andykarpov/MobyAMP/build/pdf/tda1557q_v_1_0_pcb_bottom.pdf

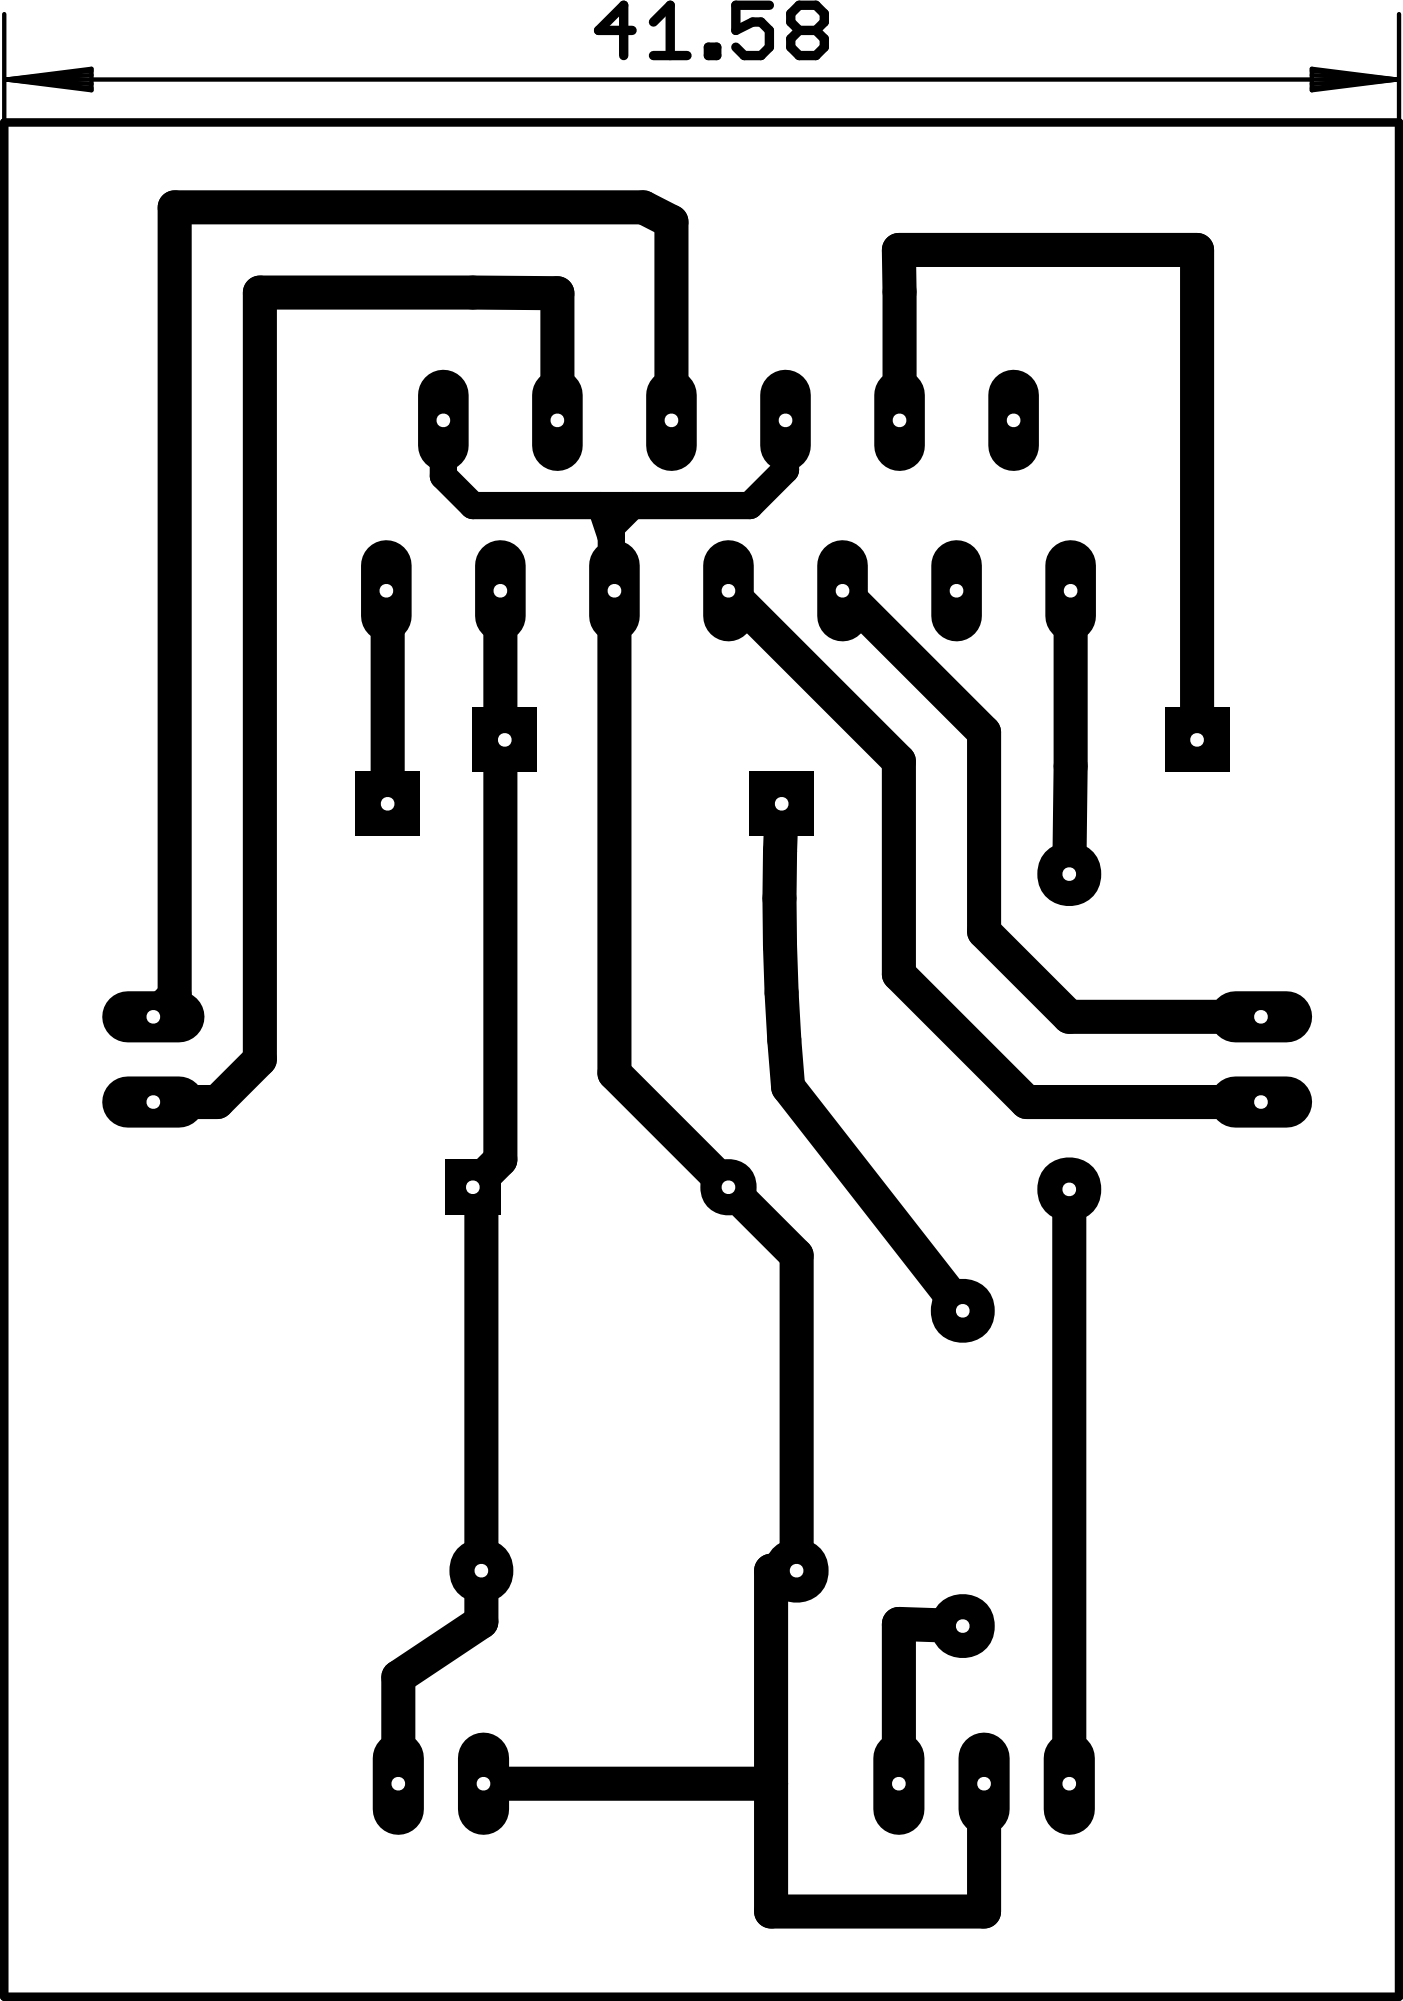
[picture p15: page 1]
