andykarpov/MobyAMP/build/pdf/tda1557q_v_1_0_pcb_cmp.pdf

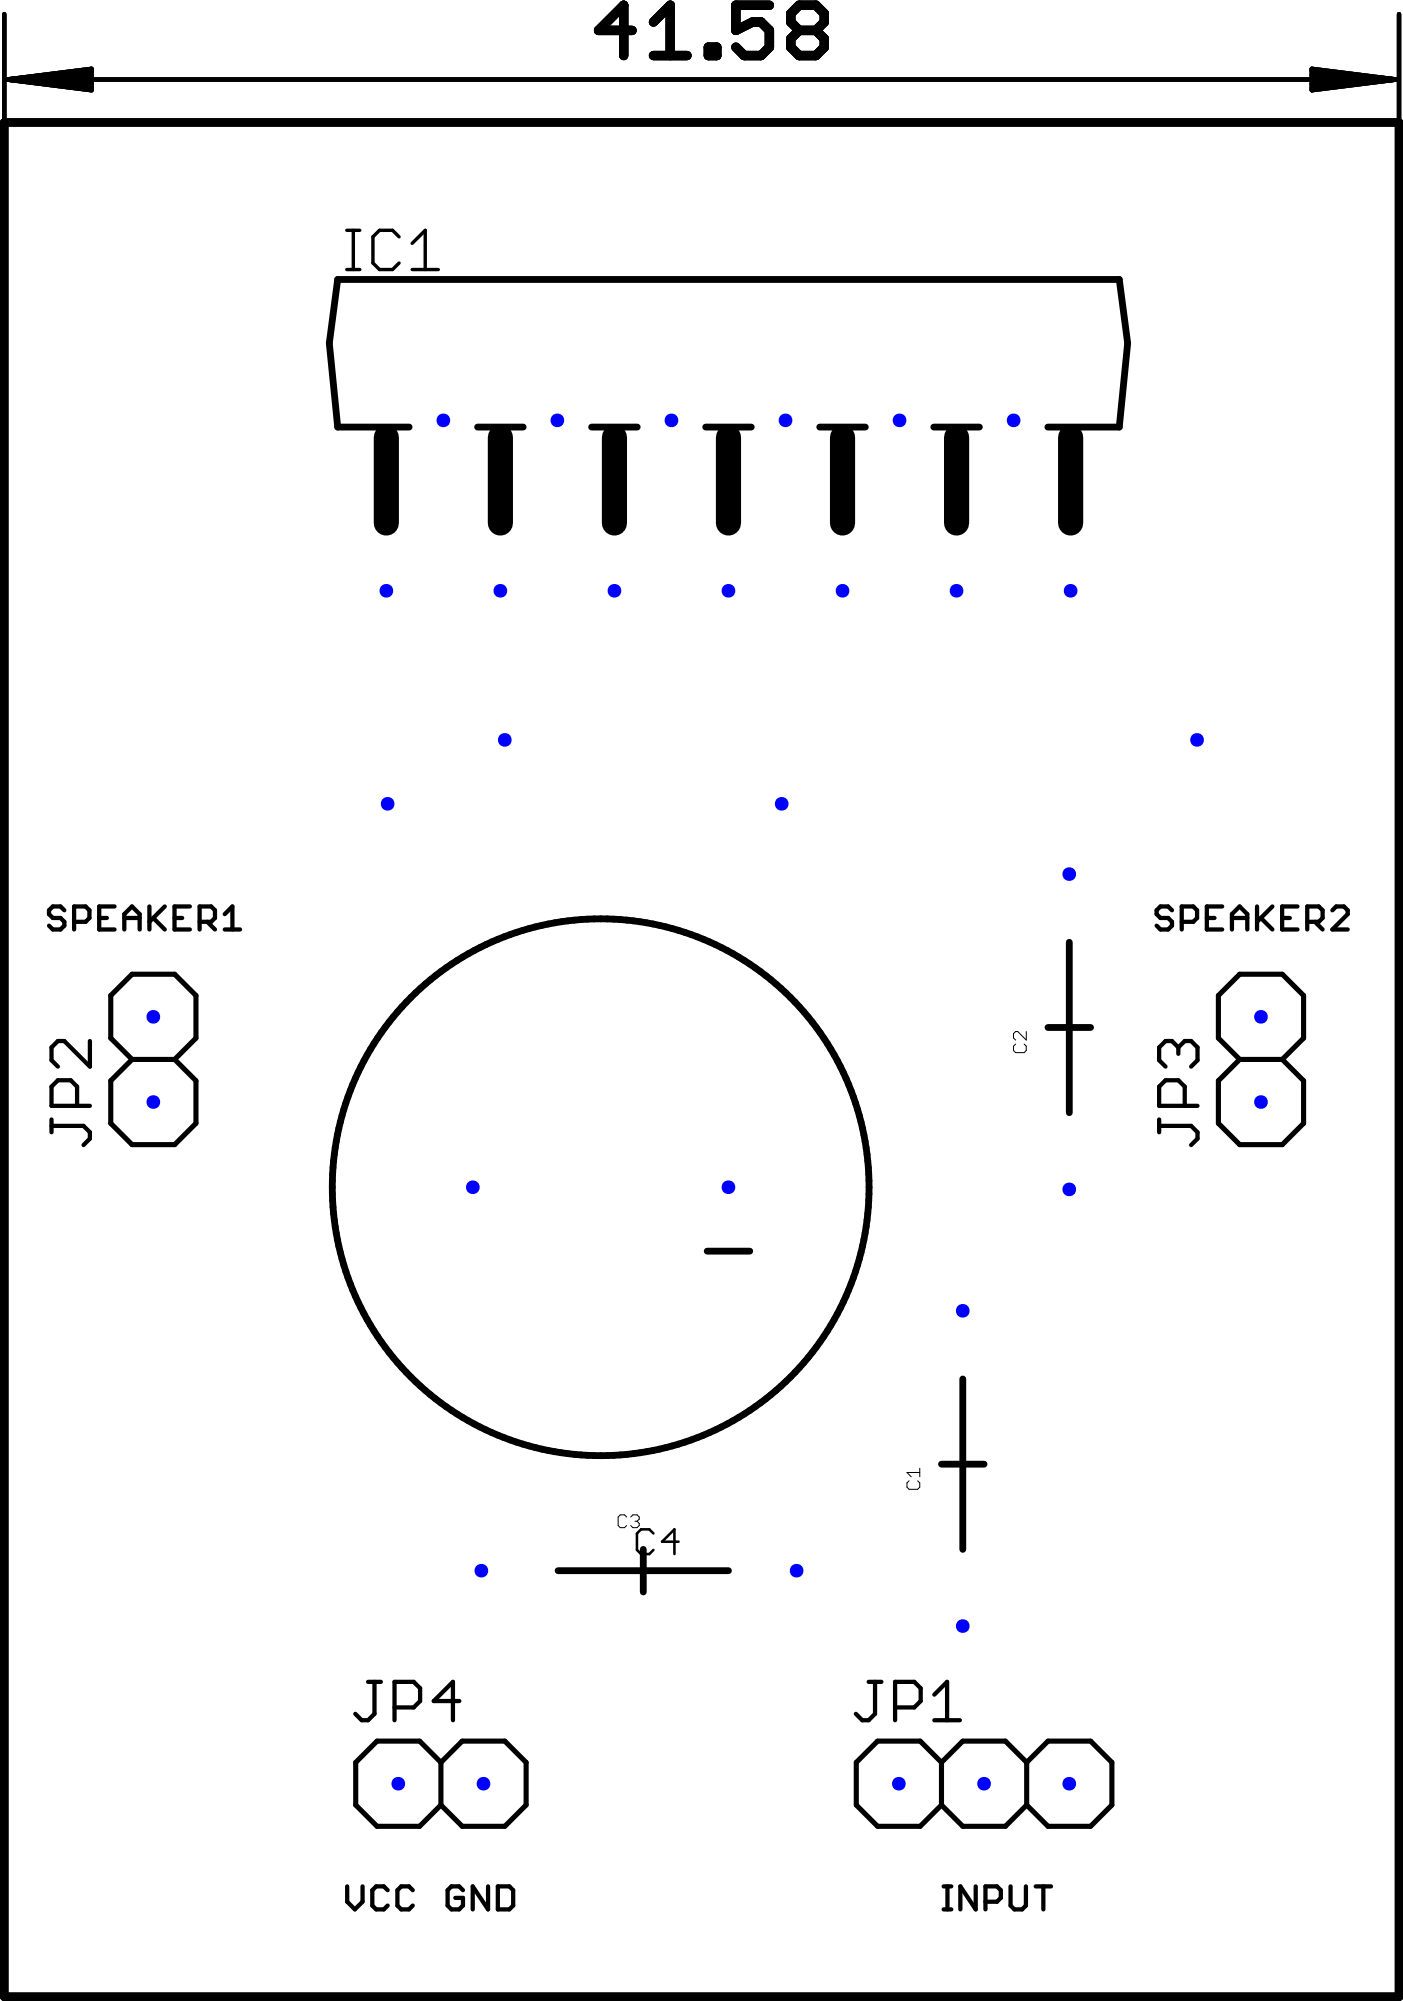
[picture p16: page 1]
