andykarpov/MobyAMP/build/pdf/tda1557q_v_1_0_pcb_top.pdf

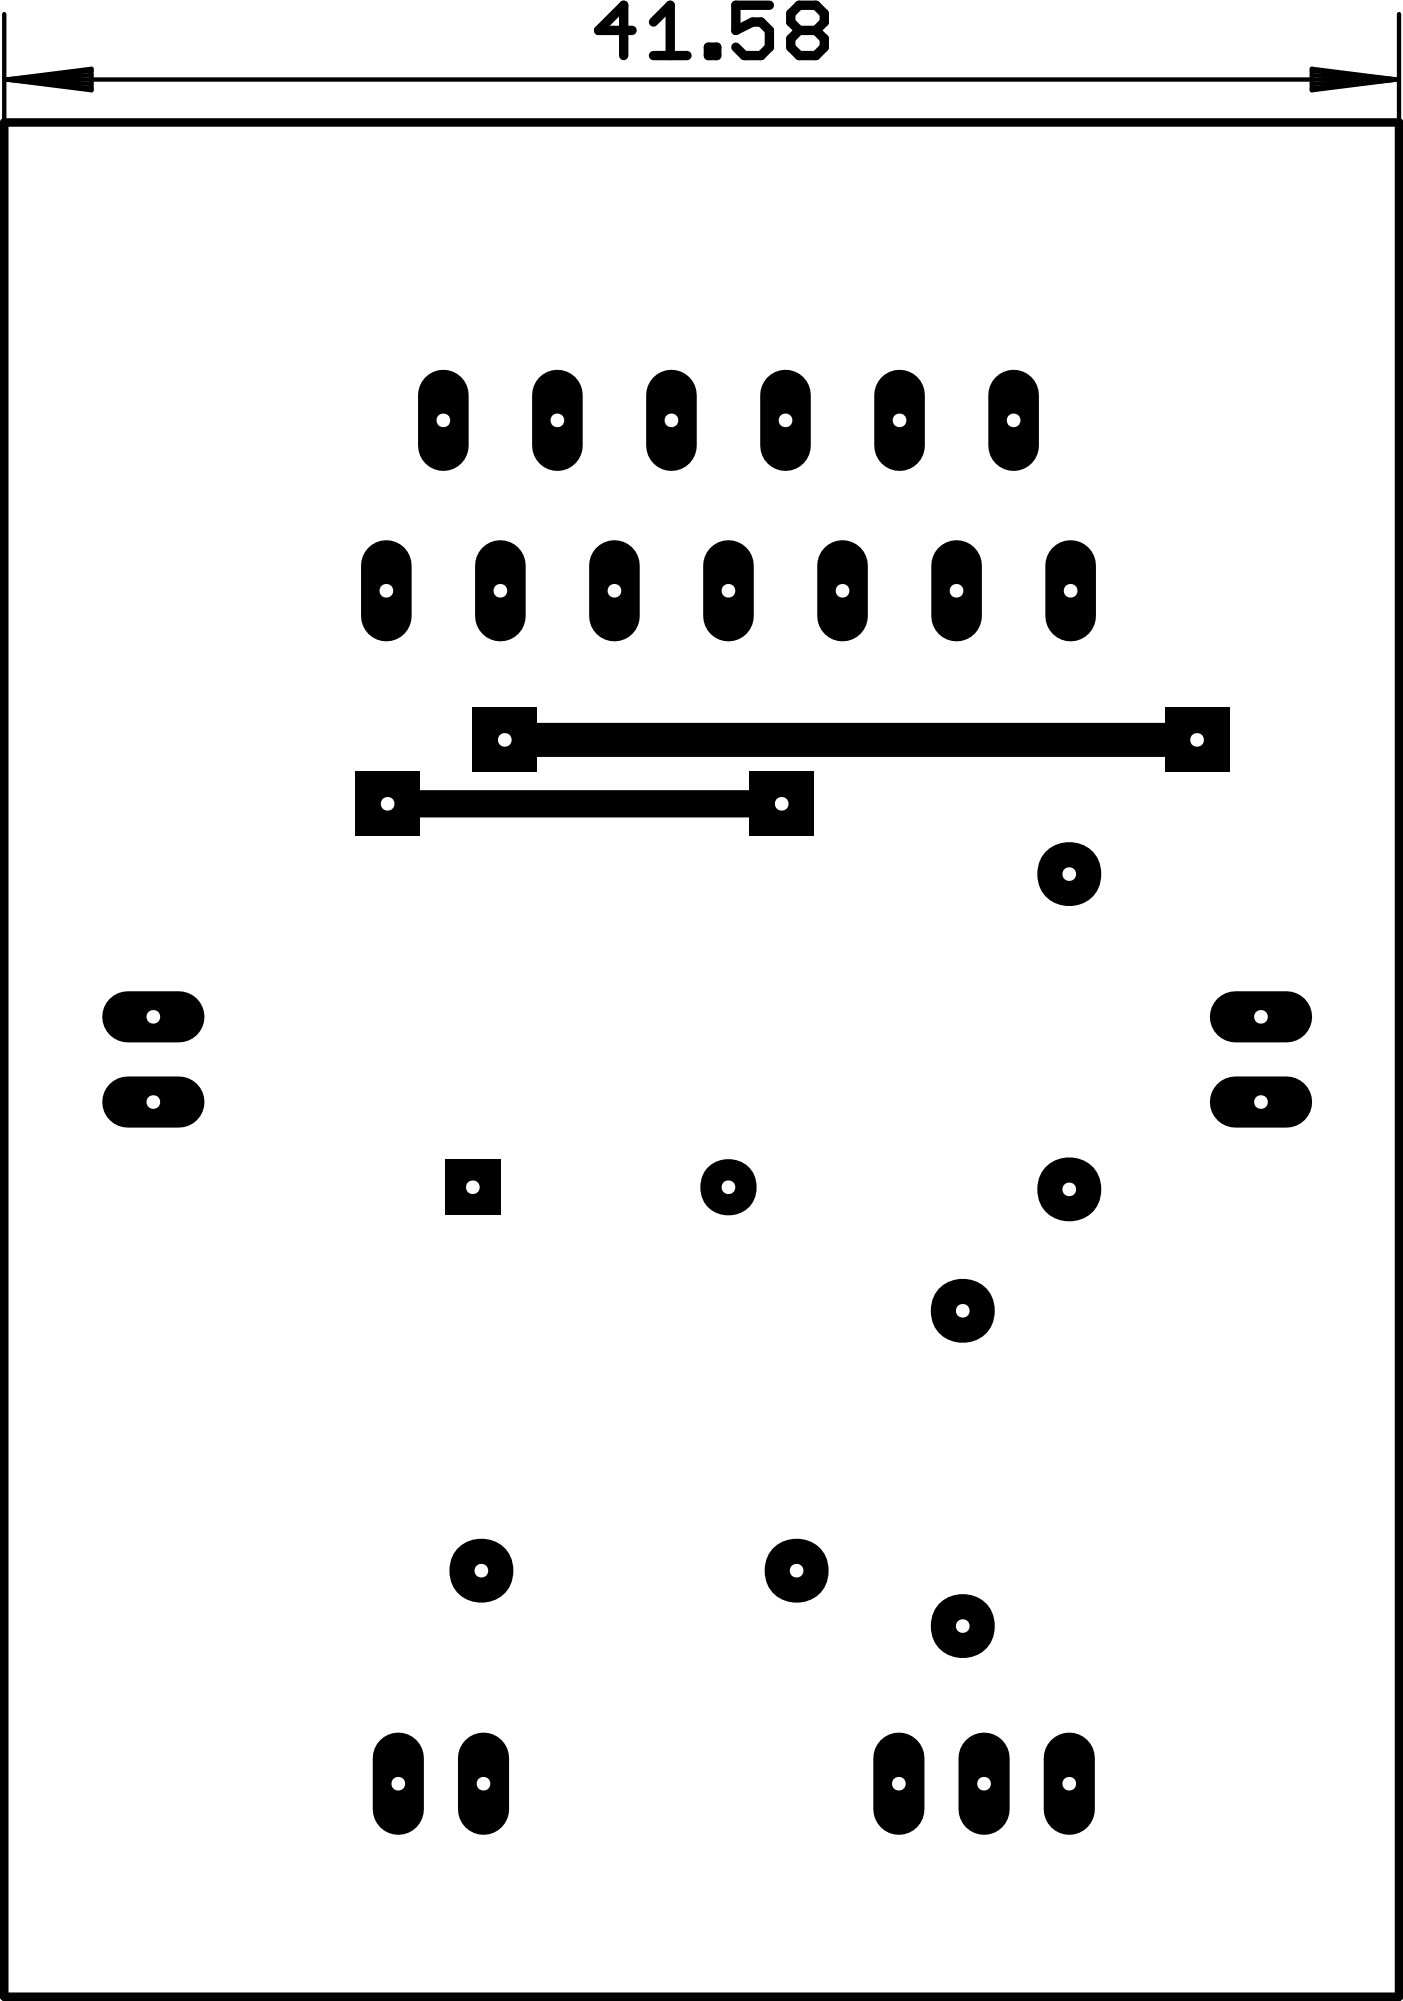
[picture p17: page 1]
