andykarpov/MobyAMP/build/pdf/tda2030a_v_1_0_pcb_bottom.pdf

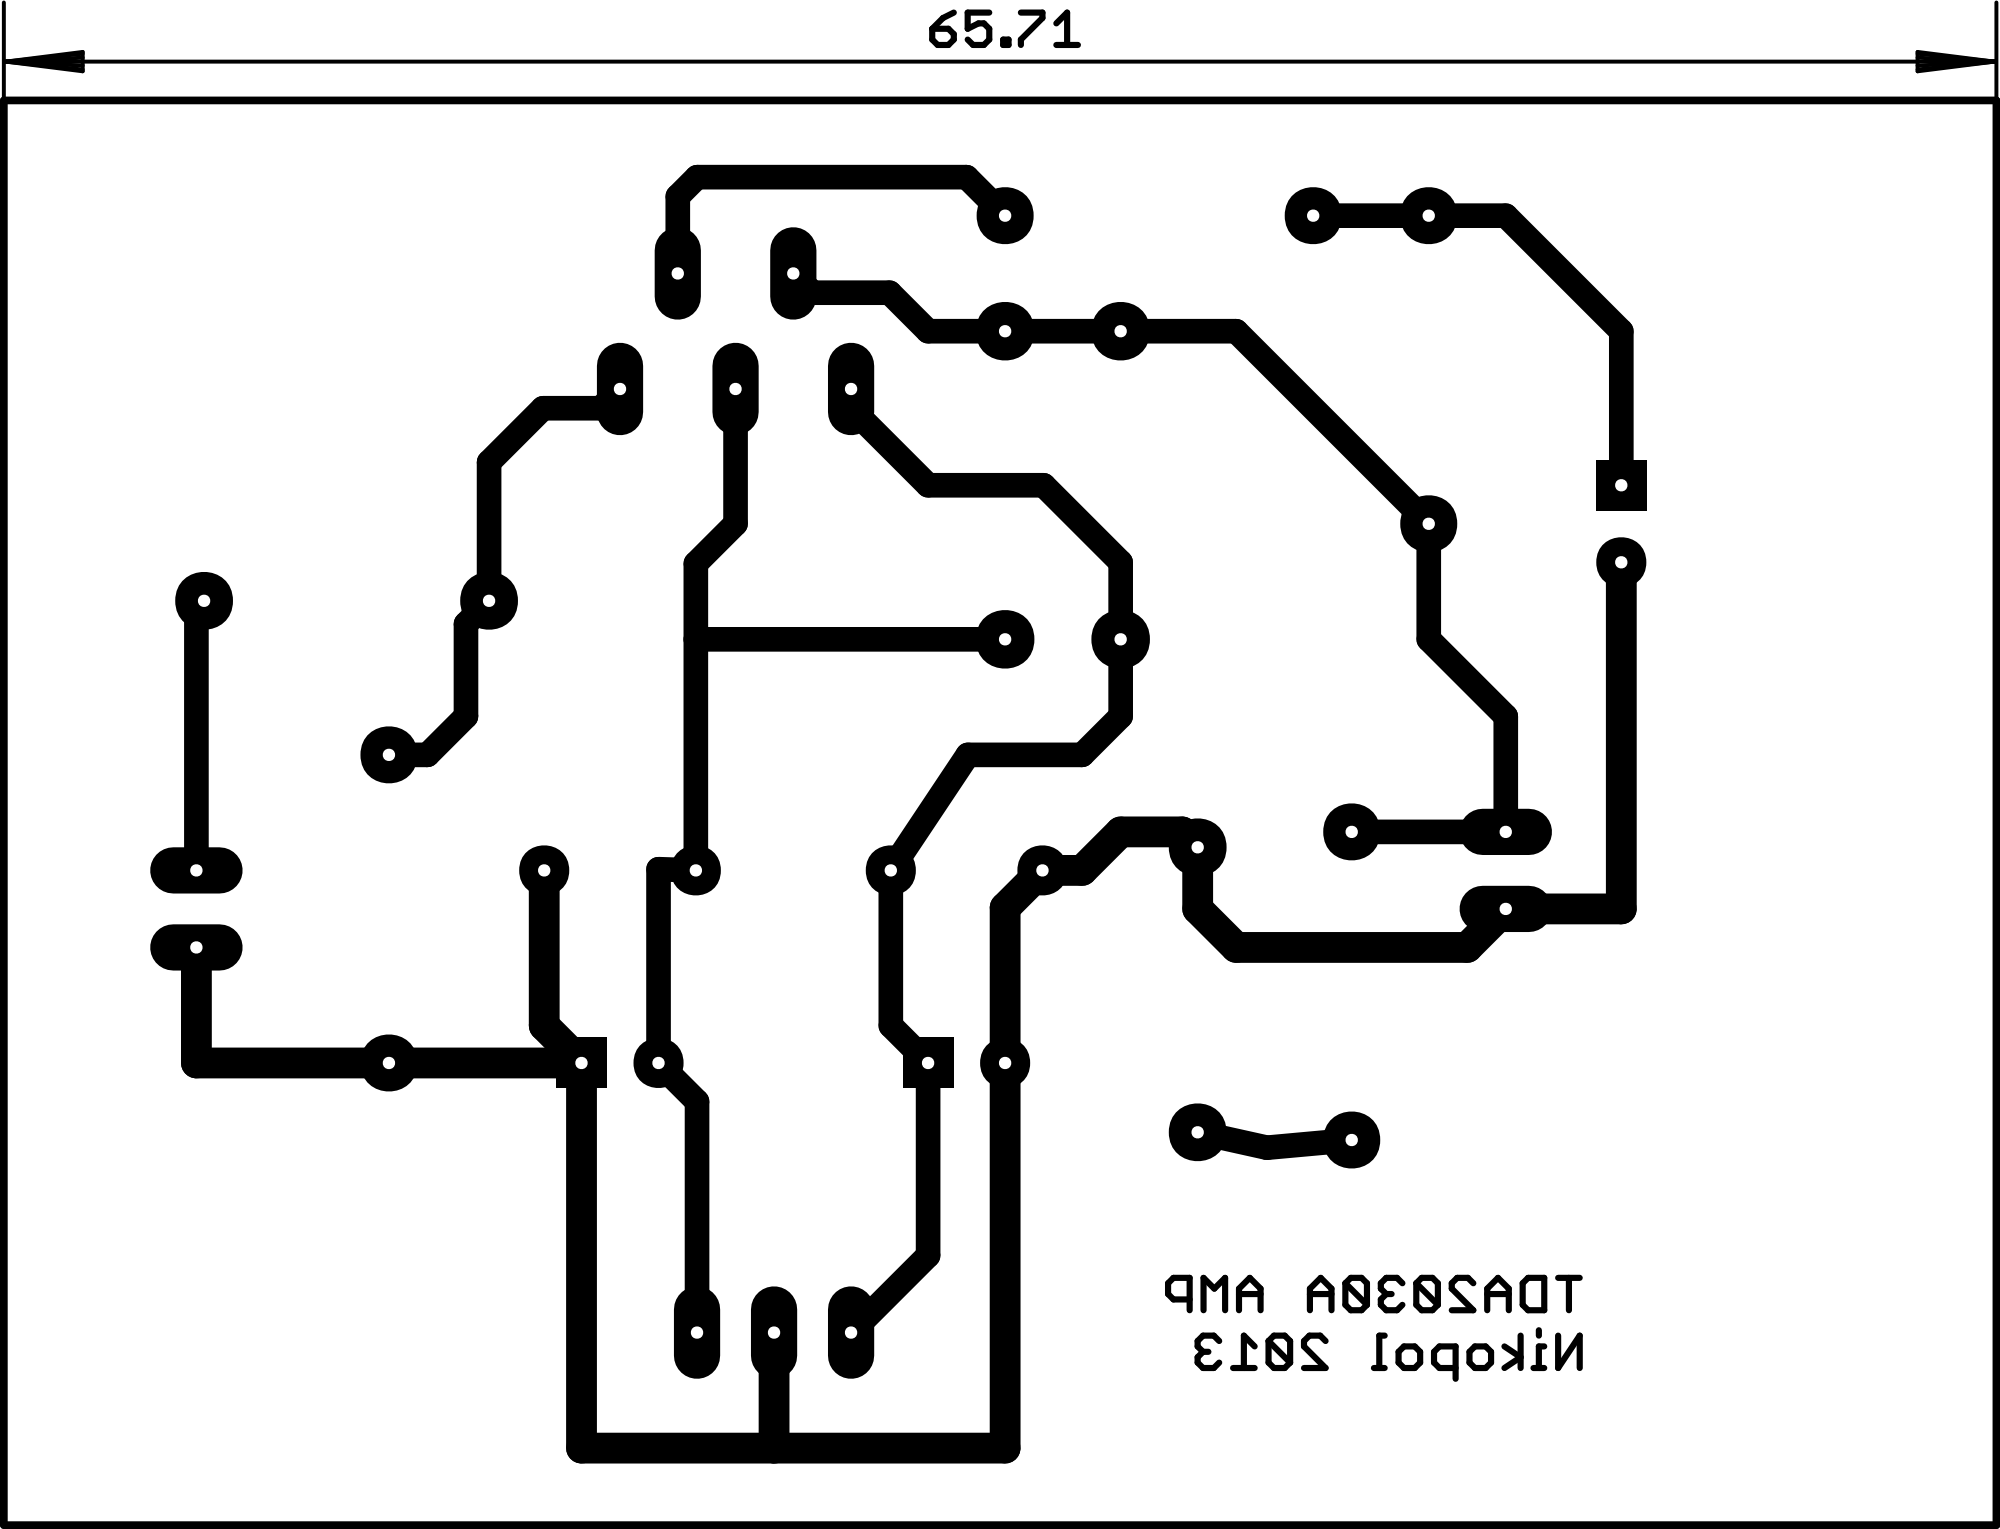
[picture p18: page 1]
