andykarpov/MobyAMP/build/pdf/tda2030a_v_1_0_pcb_cmp.pdf

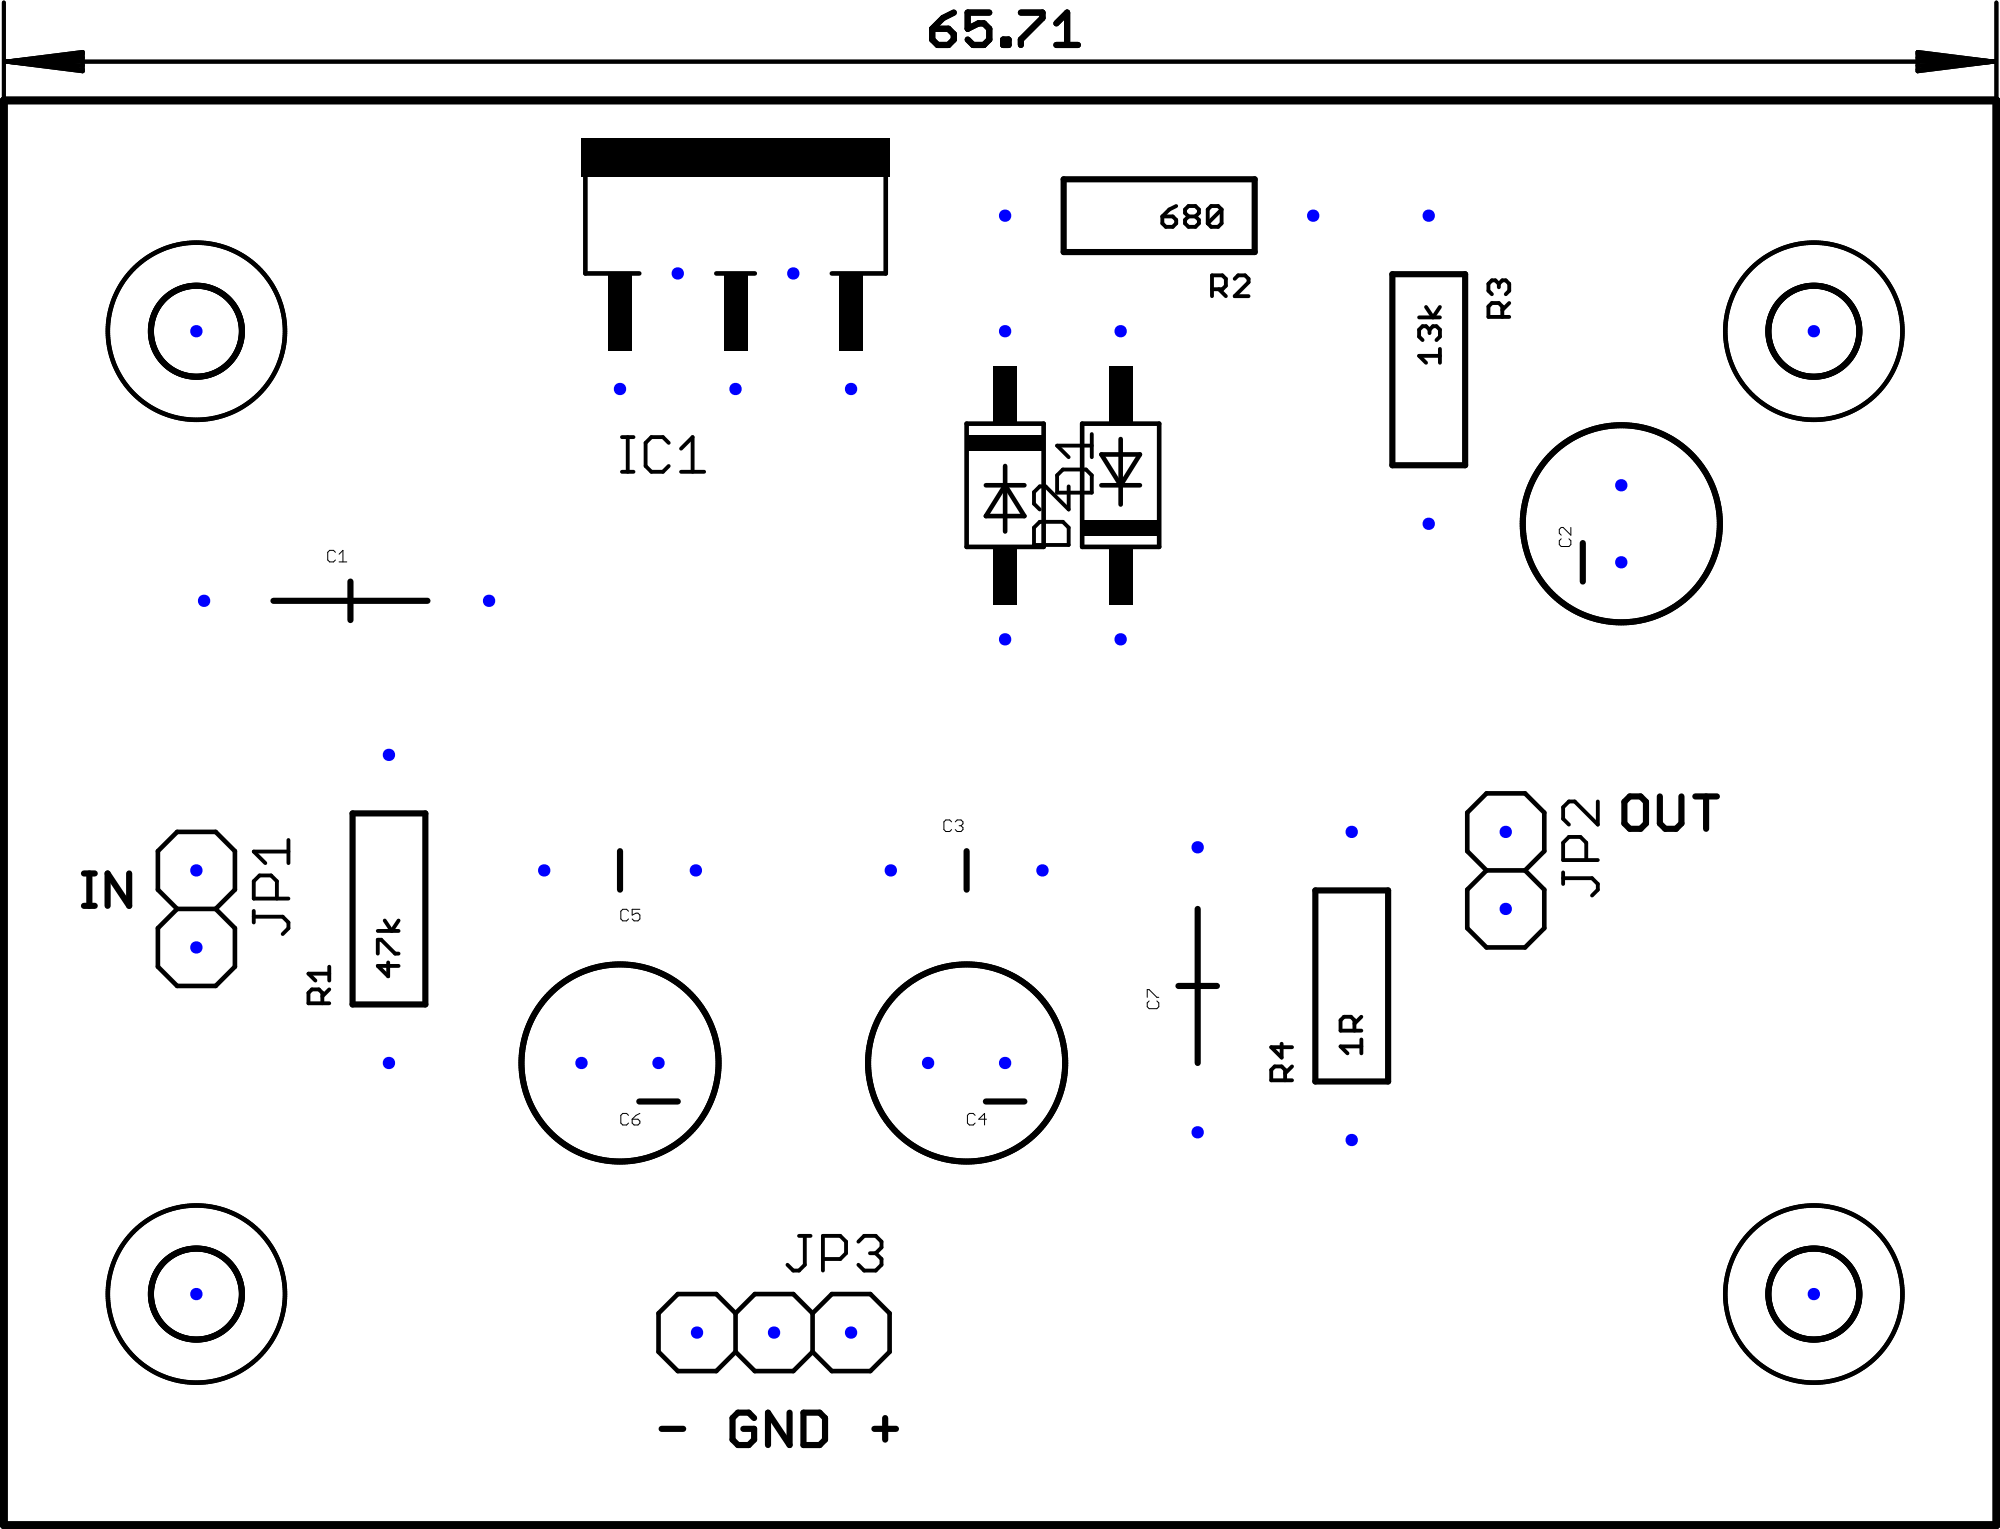
[picture p19: page 1]
