andykarpov/MobyAMP/build/pdf/tda2030a_v_1_0_pcb_top.pdf

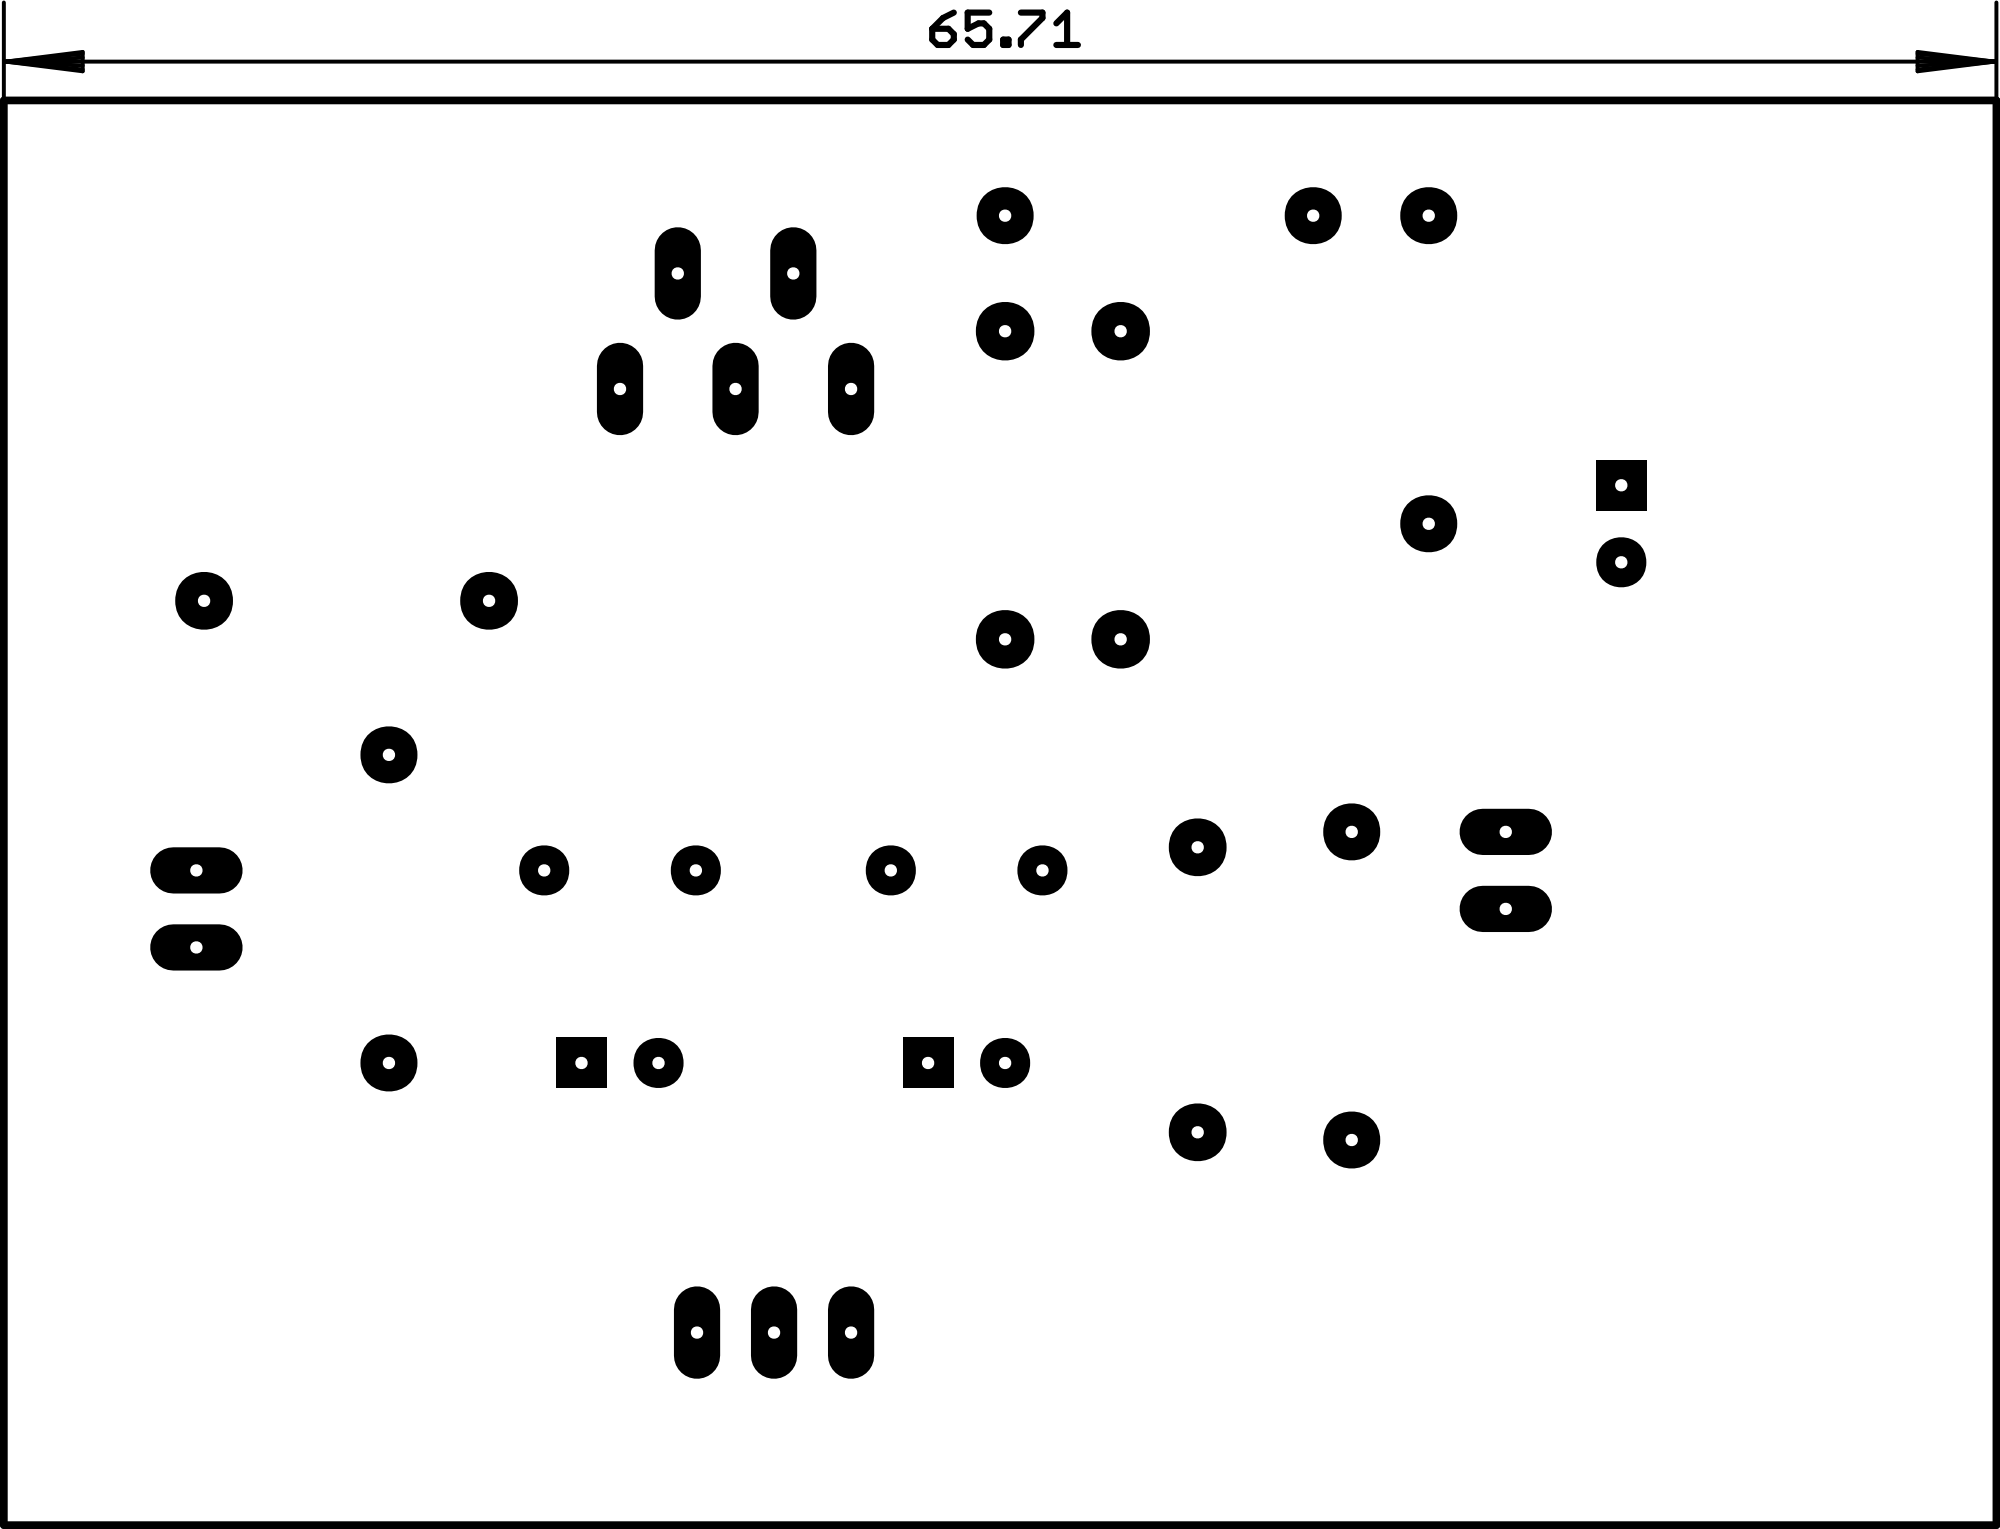
[picture p20: page 1]
