andykarpov/MobyAMP/interface2/amp_interface2_v_1_0.pdf

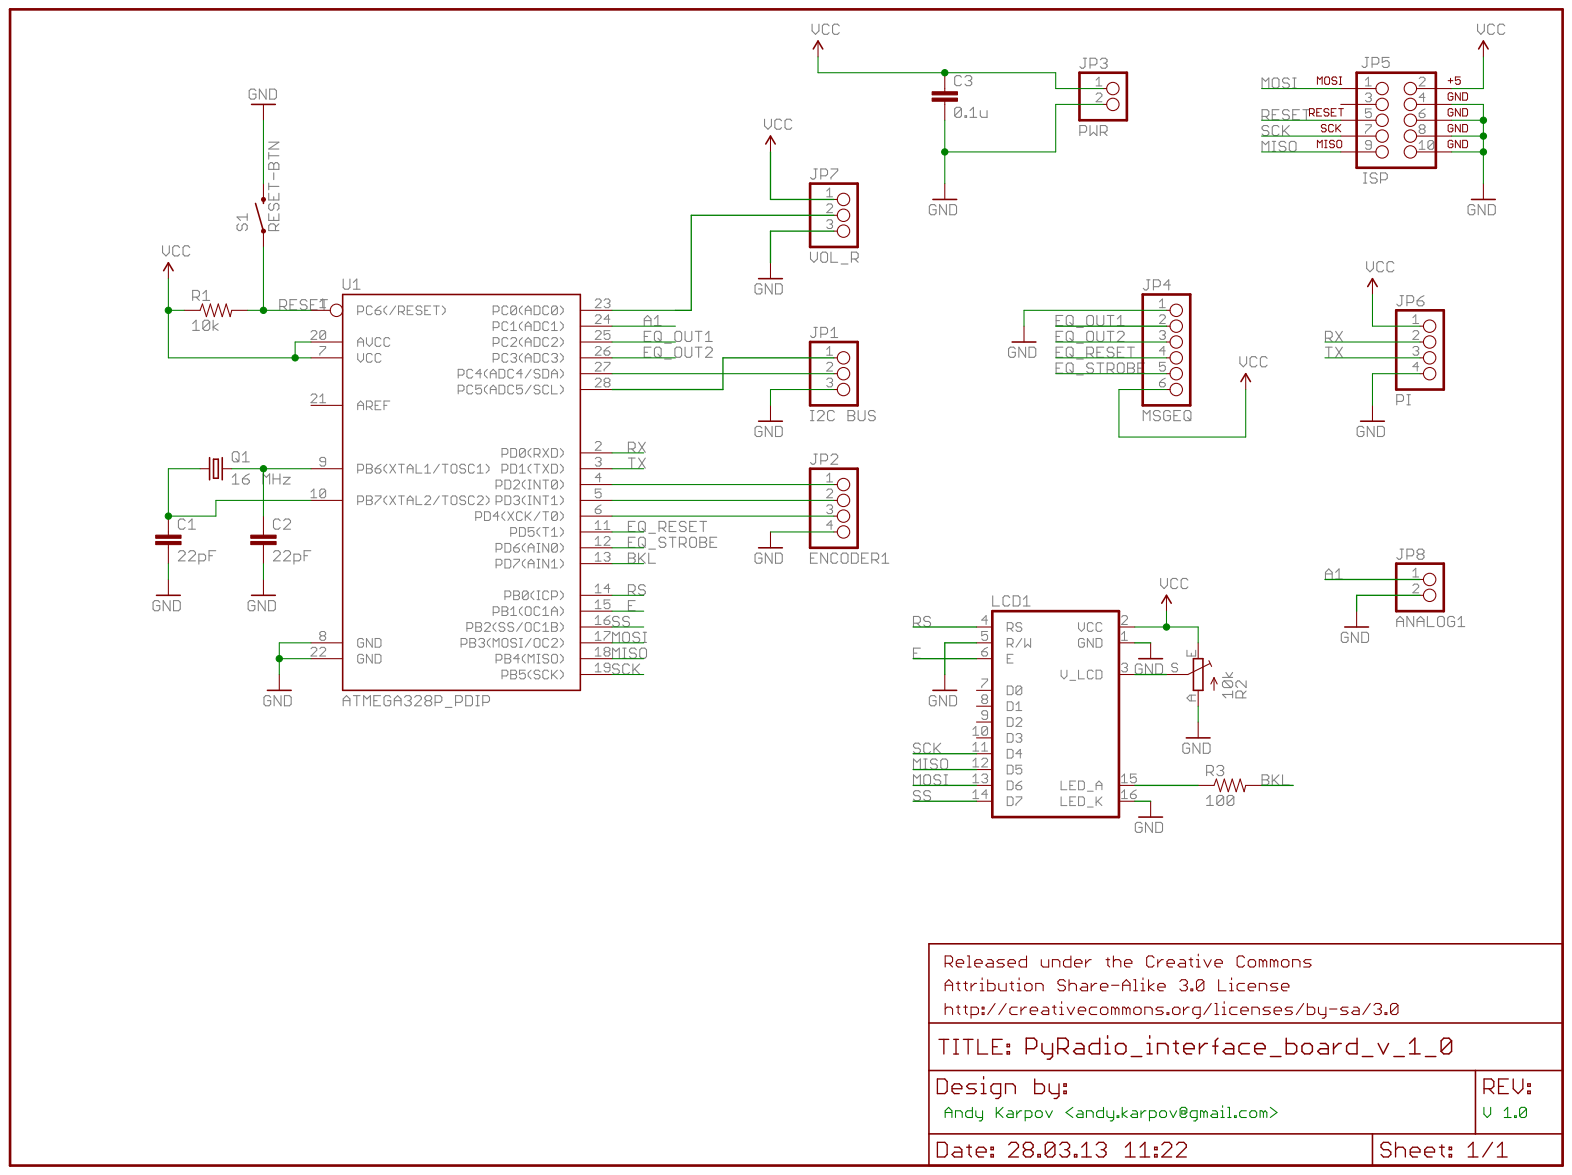
[picture p21: page 1]
