andykarpov/MobyAMP/msgeq7/amp_msgeq7_v_1_0.pdf

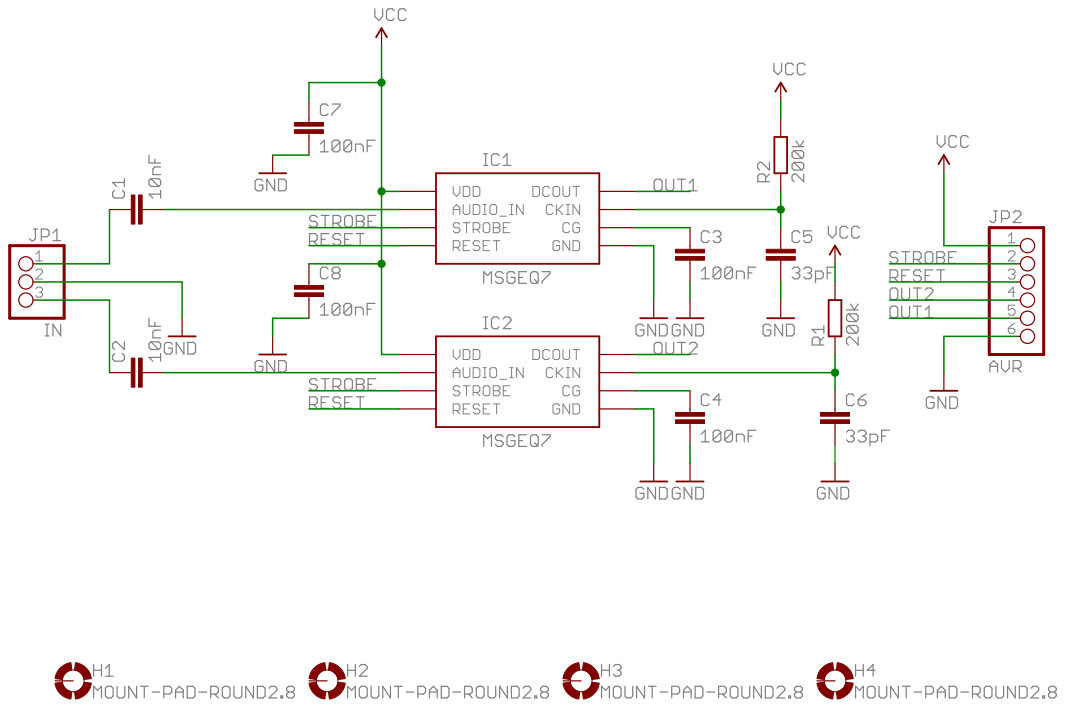
[picture p22: page 1]
