andykarpov/MobyAMP/pt2322/amp_pt2322_v_1_0.pdf

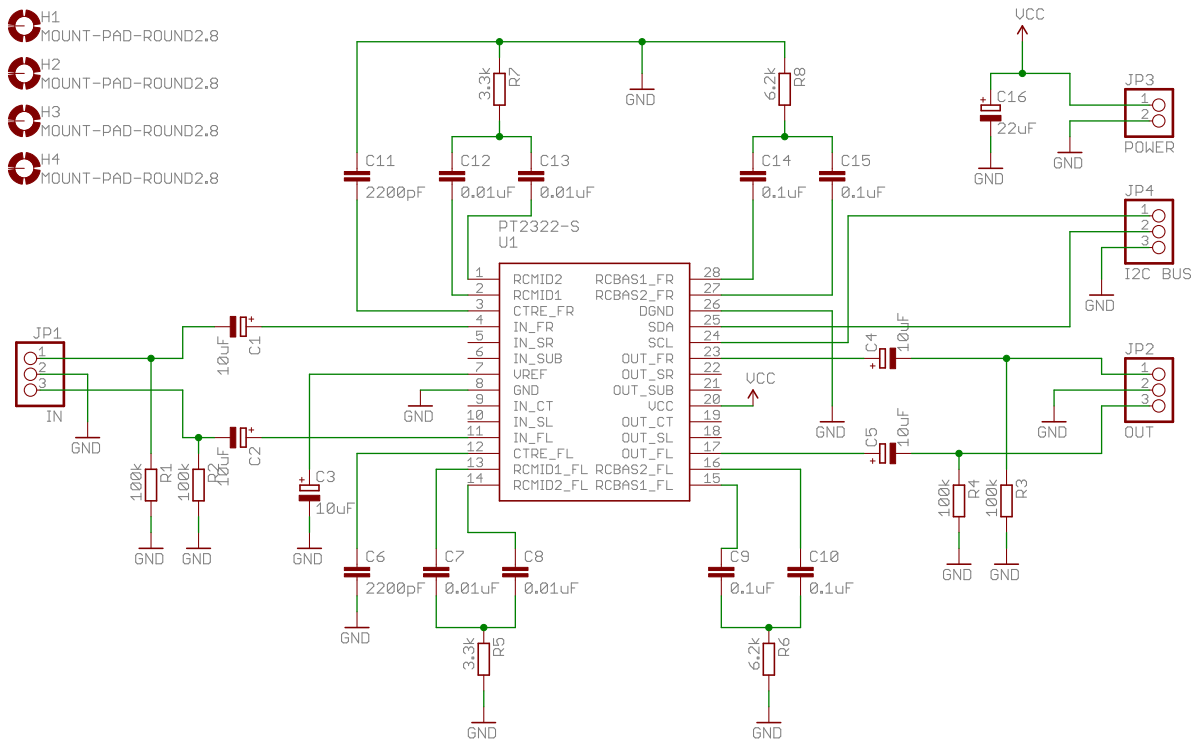
[picture p23: page 1]
