andykarpov/MobyAMP/interface/amp_interface_v_1_0.pdf

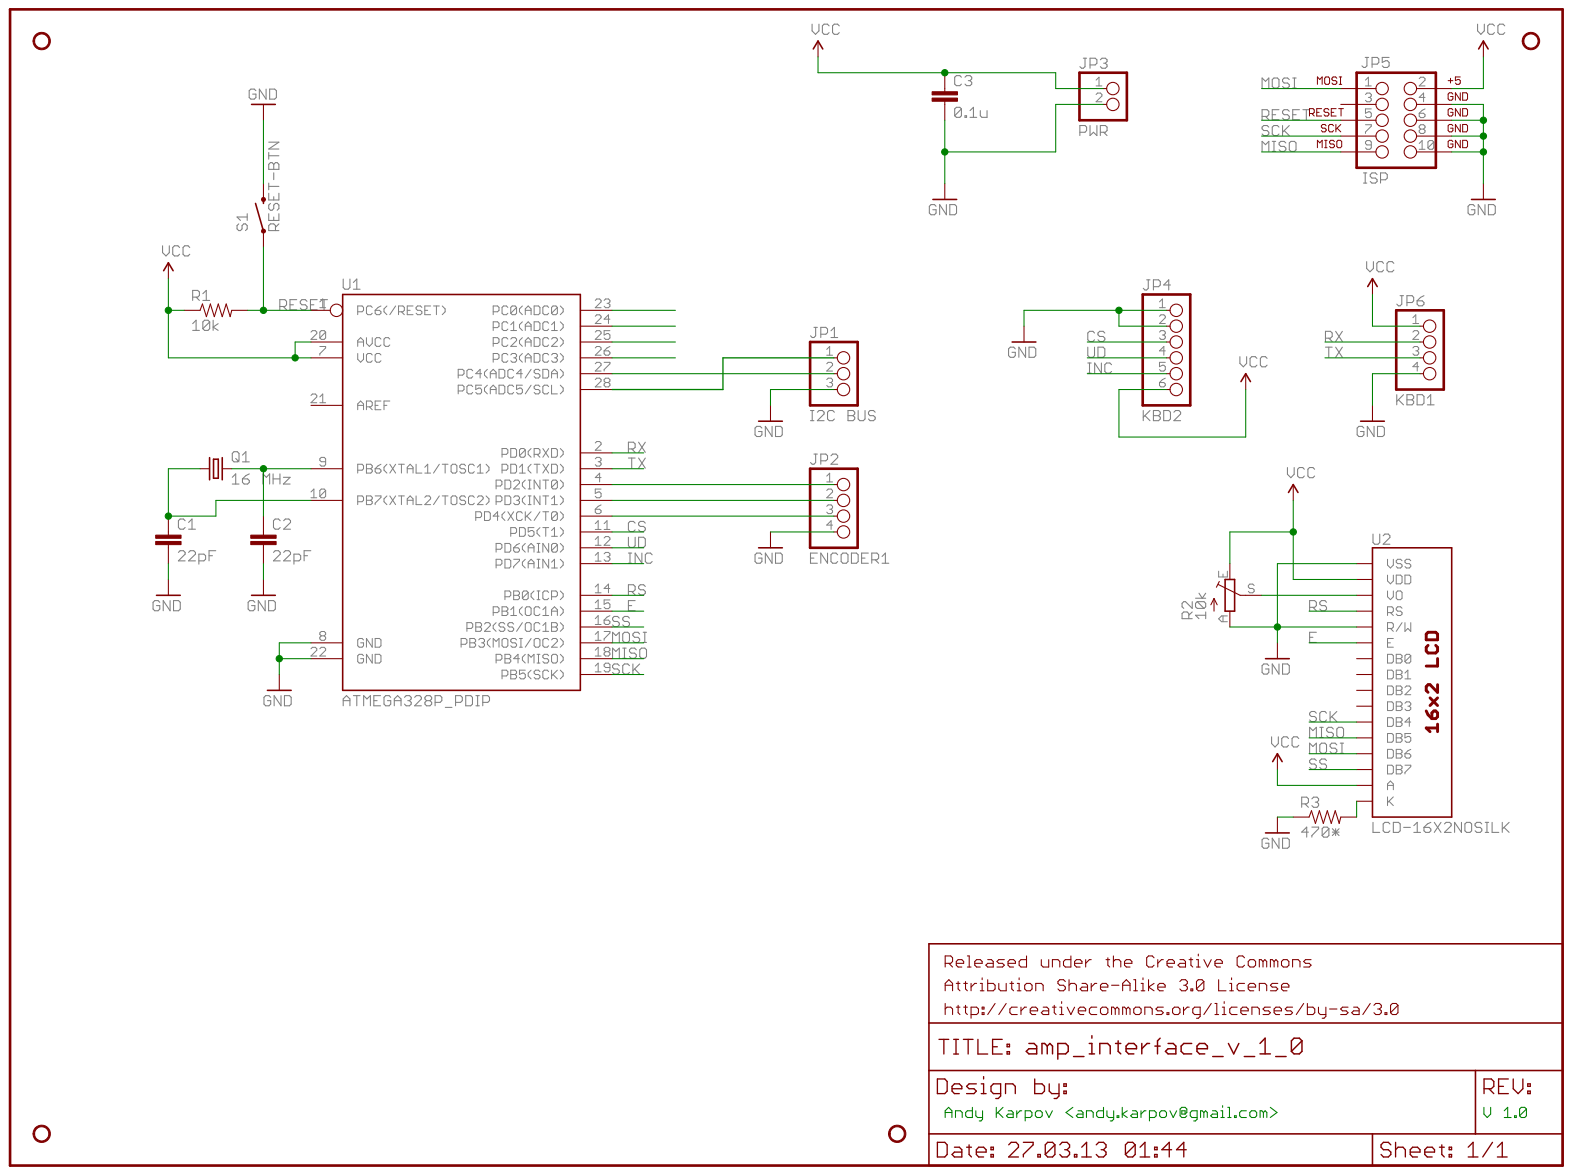
[picture p24: page 1]
