andykarpov/MobyAMP/tda1557q/amp_tda1557q_v_1_0.pdf

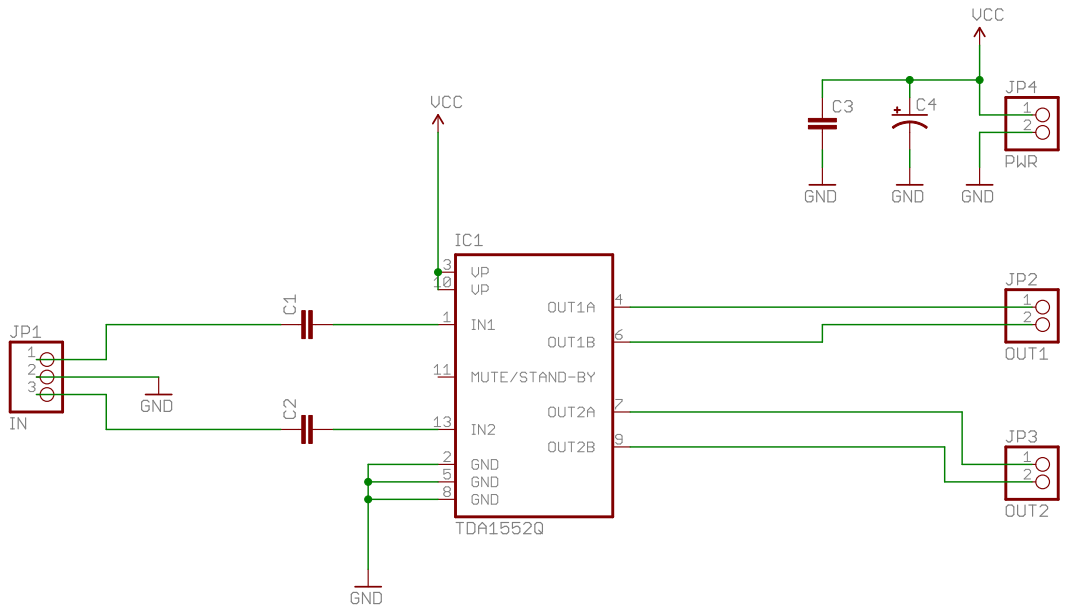
[picture p25: page 1]
