andykarpov/MobyAMP/tda2030a/amp_tda2030a_v_1_0.pdf

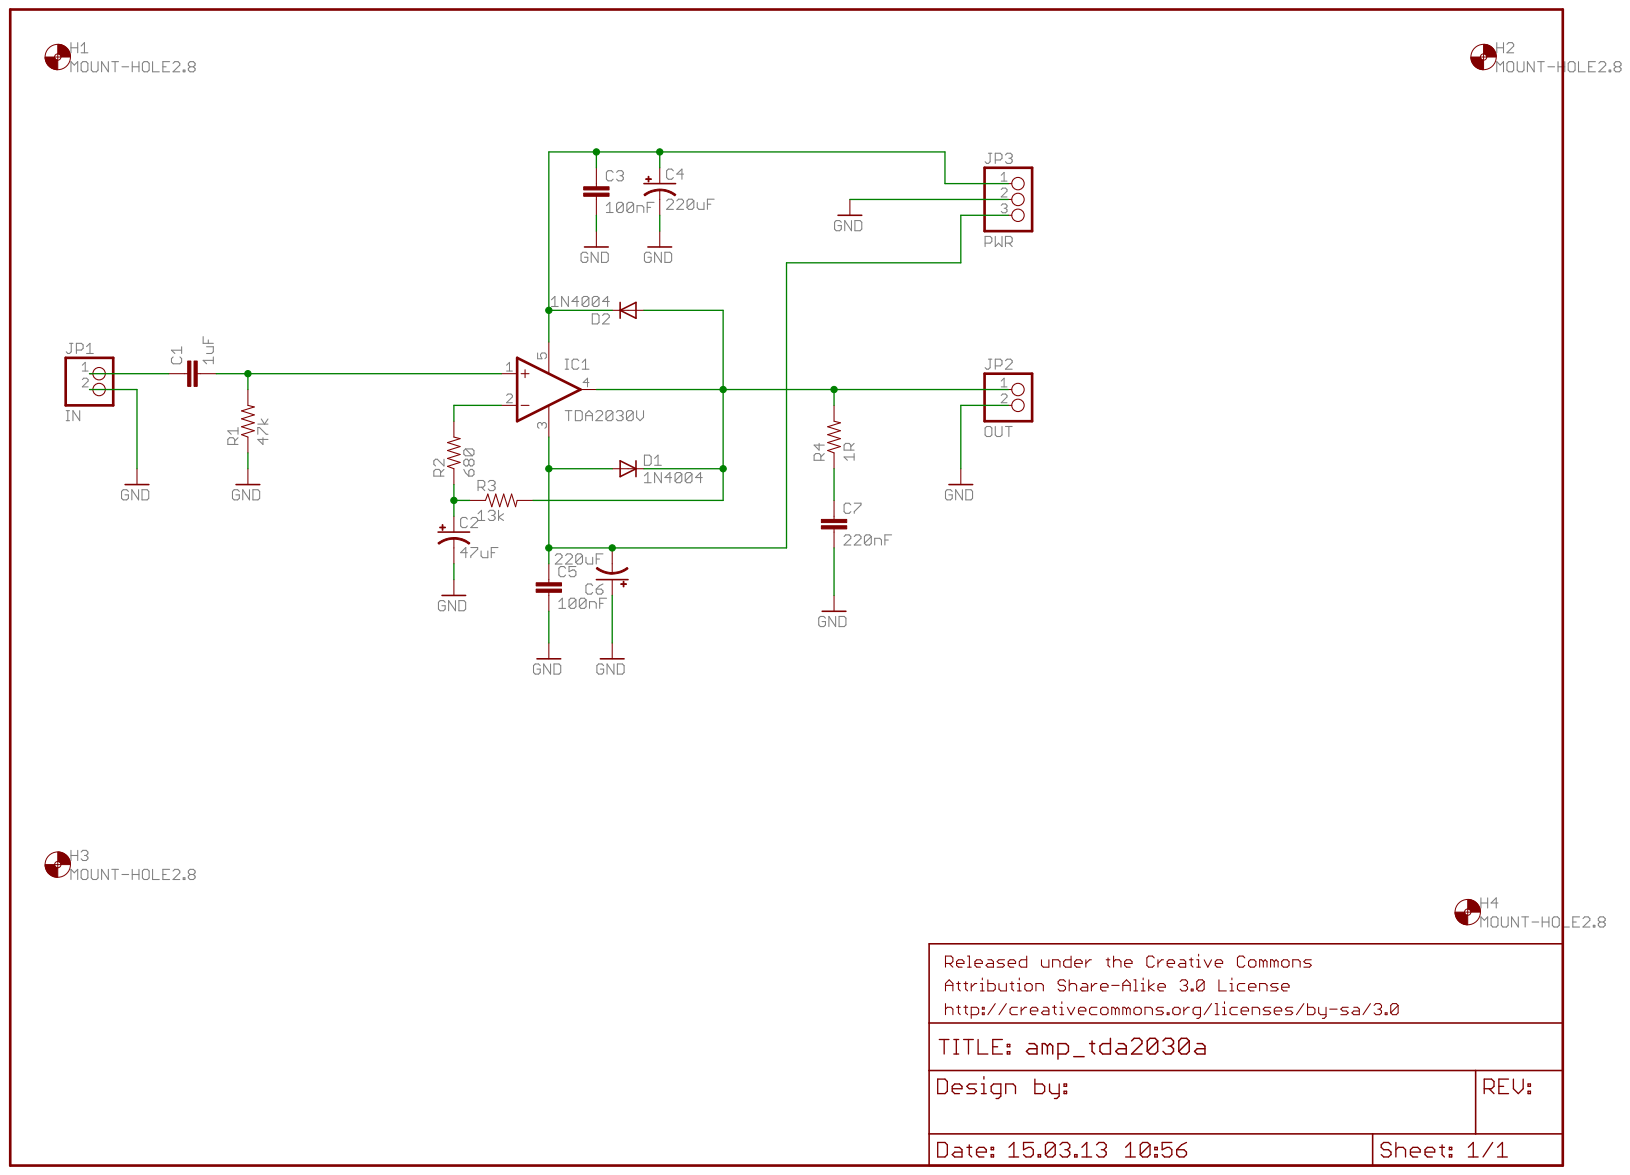
[picture p26: page 1]
