andykarpov/MobyAMP/tda8425/amp_tda8425_v_1_0.pdf

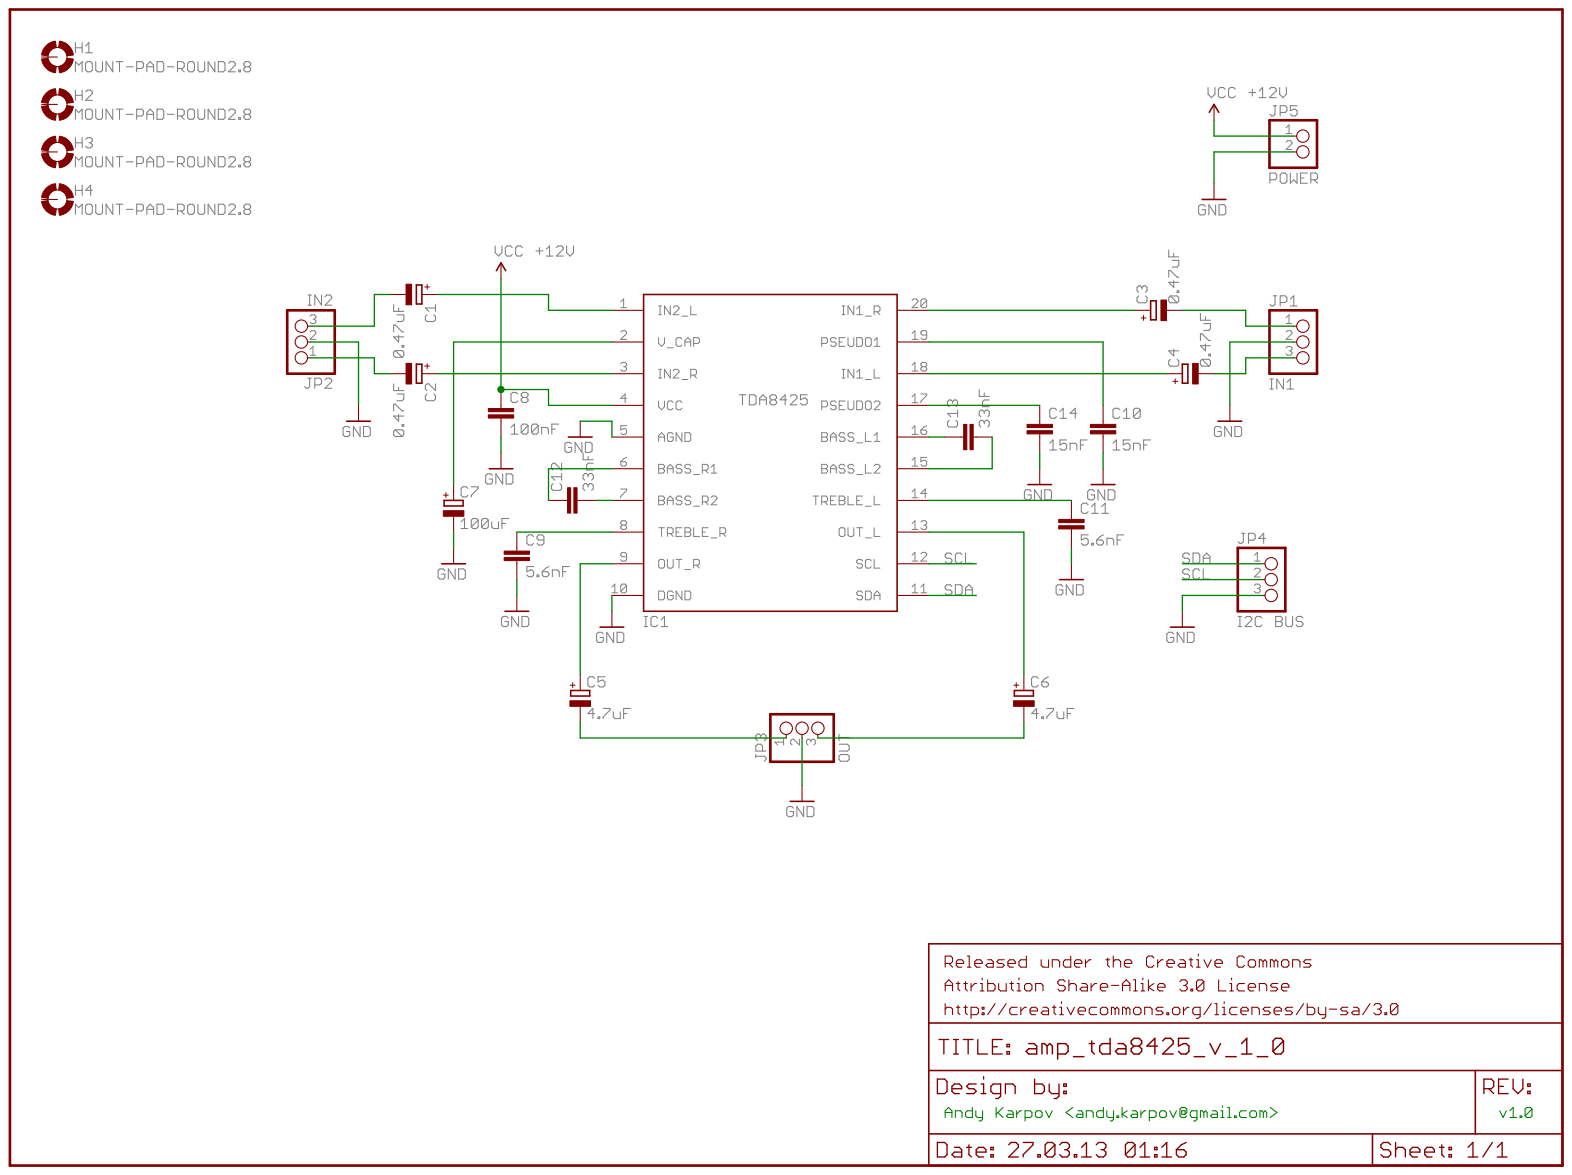
[picture p27: page 1]
